flozzone/ssr-dimmer-board/src/burst-lut.cpp

//
// Created by floz on 19/02/17.
//

#include <stdint.h>


/**
 * look-up-table for burst fire control
 *
 * use values that can be divided by 4 or 8 depending on your requirement
 * other values result in longer cycles as the load may handle
 *
 * example:
 * - 43 results in 43 cycles on and 213 cycles off
 * - 44 results in 11 cycles on and 53 cycles off
 *
 */
 /*
  *
  * TODO: TEMPORARY FIX FOR PRESENTATION!!!!
uint8_t burst_lut[256][2] = {{1,0}, {255,1}, {127,1}, {253,3}, {63,1}, {251,5}, {125,3}, {249,7}, {31,1}, {247,9},
                             {123,5}, {245,11}, {61,3}, {243,13}, {121,7}, {241,15}, {15,1}, {239,17}, {119,9}, {237,19},
                             {59,5}, {235,21}, {117,11}, {233,23}, {29,3}, {231,25}, {115,13}, {229,27}, {57,7}, {227,29},
                             {113,15}, {225,31}, {7,1}, {223,33}, {111,17}, {221,35}, {55,9}, {219,37}, {109,19}, {217,39},
                             {27,5}, {215,41}, {107,21}, {213,43}, {53,11}, {211,45}, {105,23}, {209,47}, {13,3},
                             {207,49}, {103,25}, {205,51}, {51,13}, {203,53}, {101,27}, {201,55}, {25,7}, {199,57}, {99,29},
                             {197,59}, {49,15}, {195,61}, {97,31}, {193,63}, {3,1}, {191,65}, {95,33}, {189,67},
                             {47,17}, {187,69}, {93,35}, {185,71}, {23,9}, {183,73}, {91,37}, {181,75}, {45,19},
                             {179,77}, {89,39}, {177,79}, {11,5}, {175,81}, {87,41}, {173,83}, {43,21}, {171,85},
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
                            {7,9},
                            {6,10},
                            {5,11},
                            {4,12},
                            {3,13},
                            {2,14},
                            {1,15},
                            {0,16}};
